golaced/Moco-8-OpenSourced-Quadruped-Robot/support_file/img_file1/a8.jpg

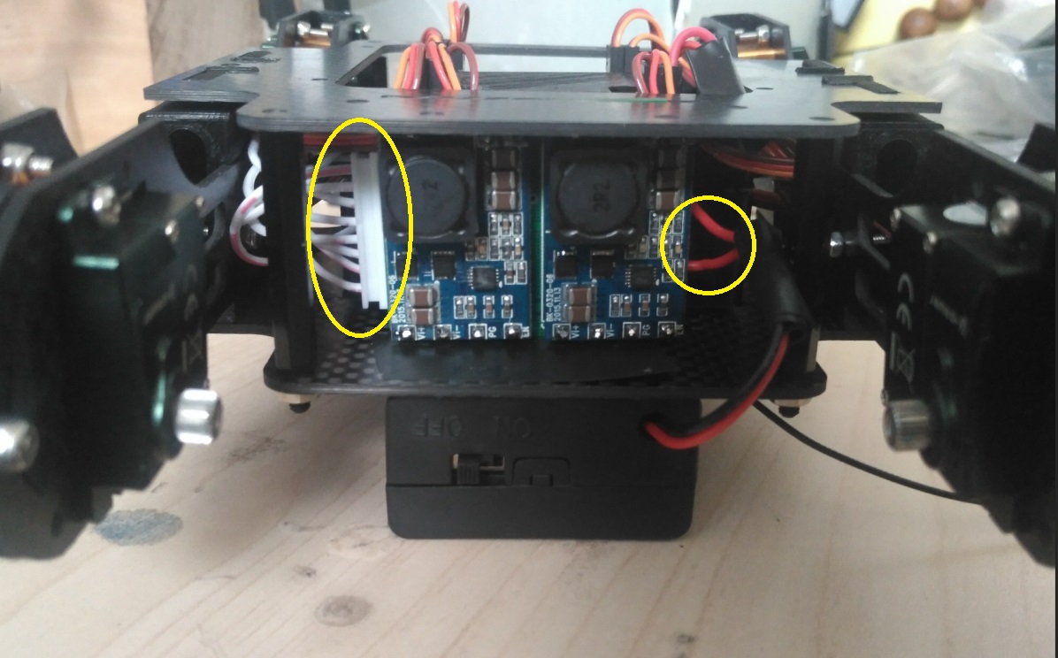
support_file/img_file1/a8.jpg
