golaced/Moco-8-OpenSourced-Quadruped-Robot/support_file/img_file1/a10.JPG

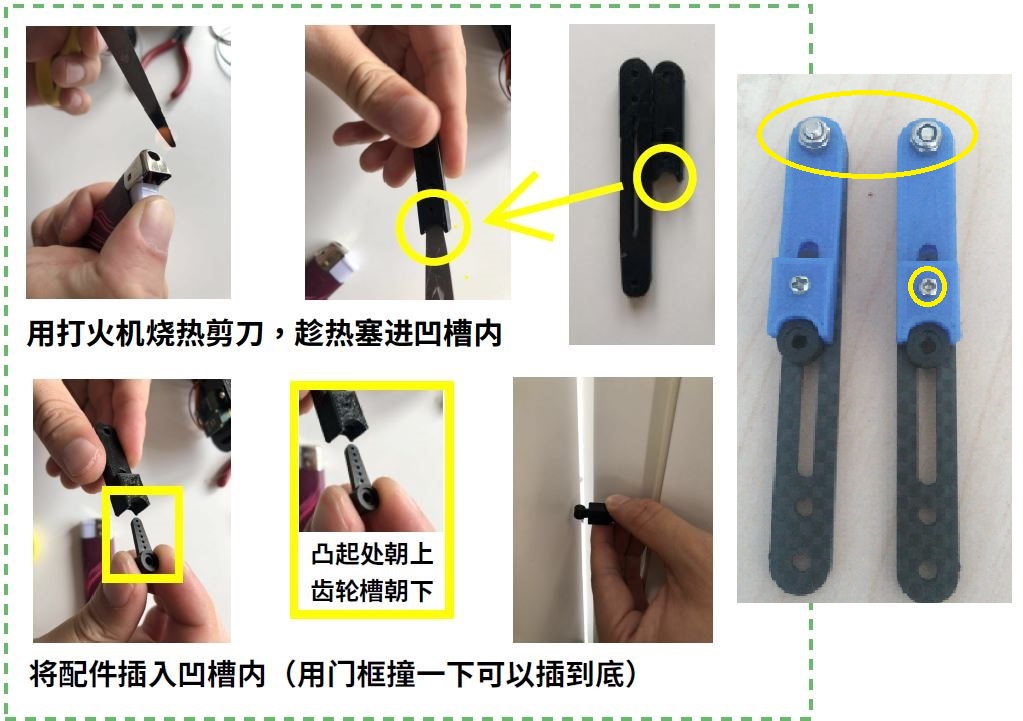
support_file/img_file1/a10.JPG
