golaced/Moco-8-OpenSourced-Quadruped-Robot/support_file/img_file1/fc5.jpg

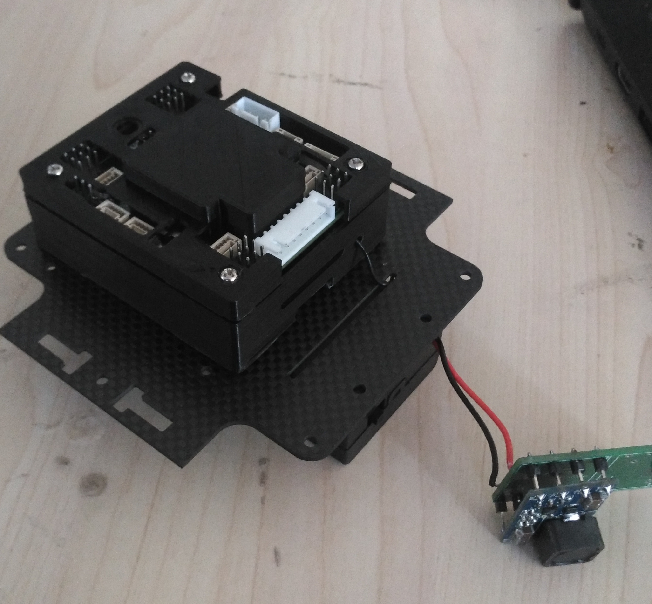
support_file/img_file1/fc5.jpg
