golaced/Moco-8-OpenSourced-Quadruped-Robot/support_file/img_file1/leg_end.jpg

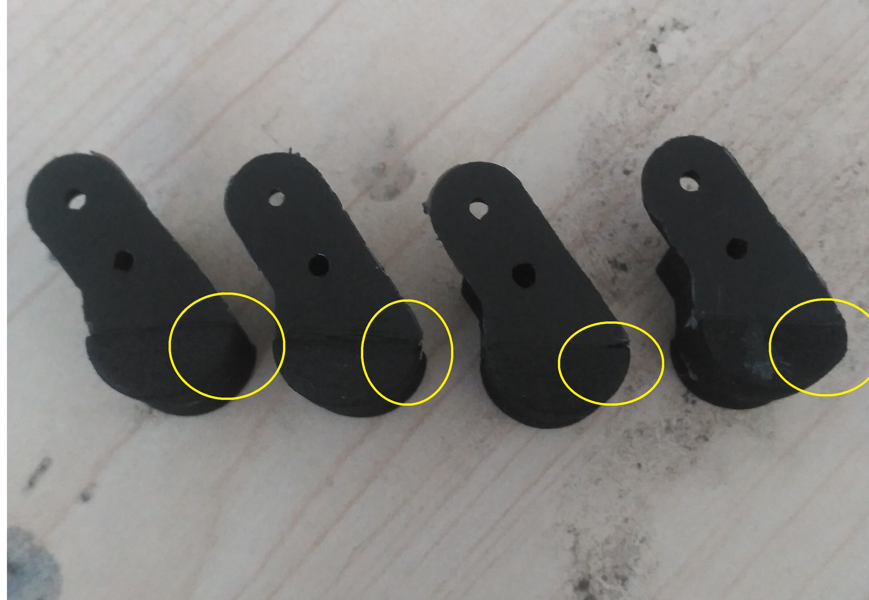
support_file/img_file1/leg_end.jpg
