golaced/Moco-8-OpenSourced-Quadruped-Robot/support_file/img_file/cap2.JPG

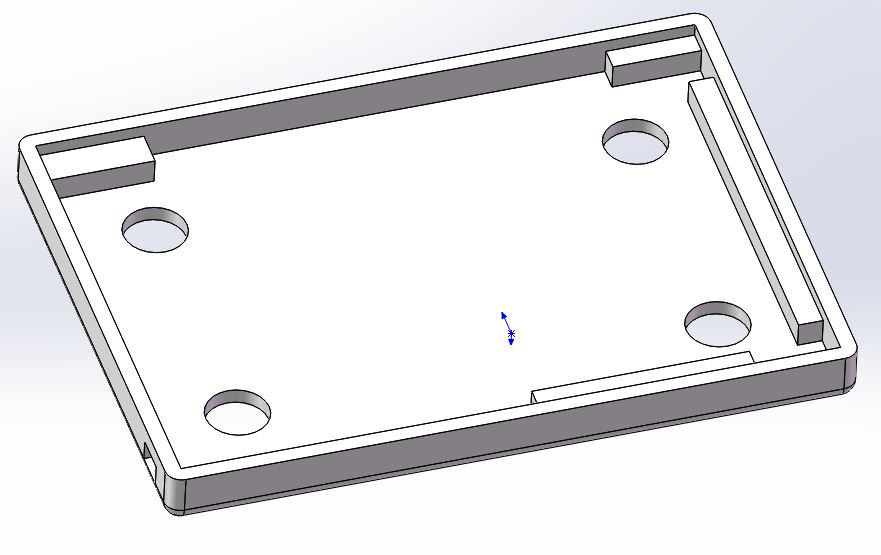
support_file/img_file/cap2.JPG
