golaced/Moco-8-OpenSourced-Quadruped-Robot/support_file/img_file/cap3.JPG

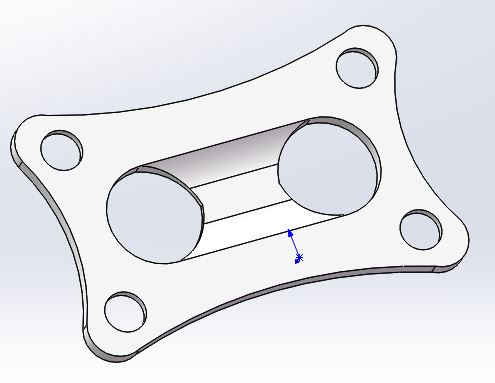
support_file/img_file/cap3.JPG
