golaced/Moco-8-OpenSourced-Quadruped-Robot/support_file/img_file/CH.jpg

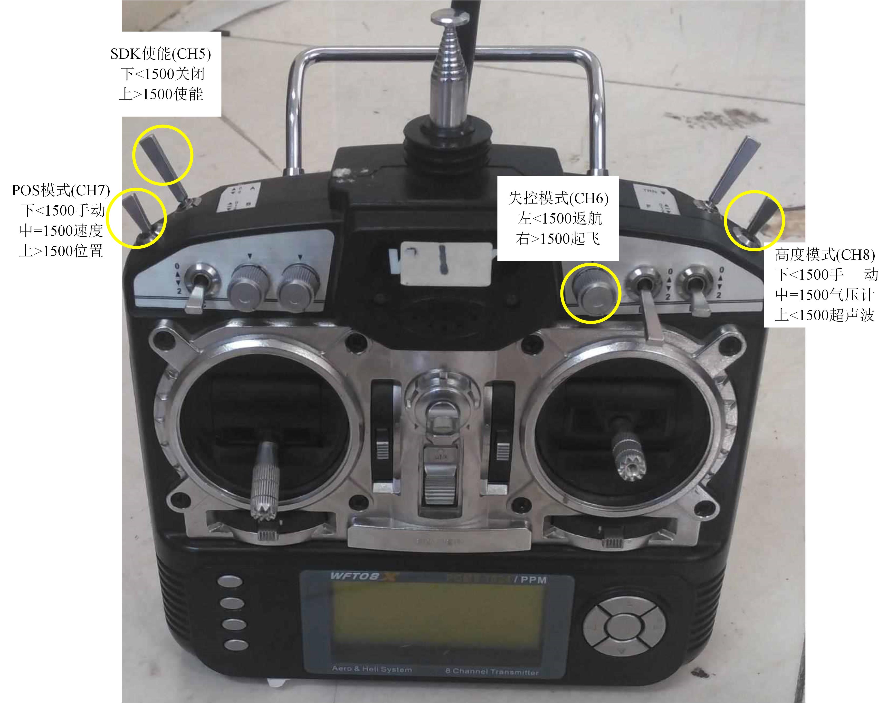
support_file/img_file/CH.jpg
