golaced/Moco-8-OpenSourced-Quadruped-Robot/support_file/img_file/dmz.JPG

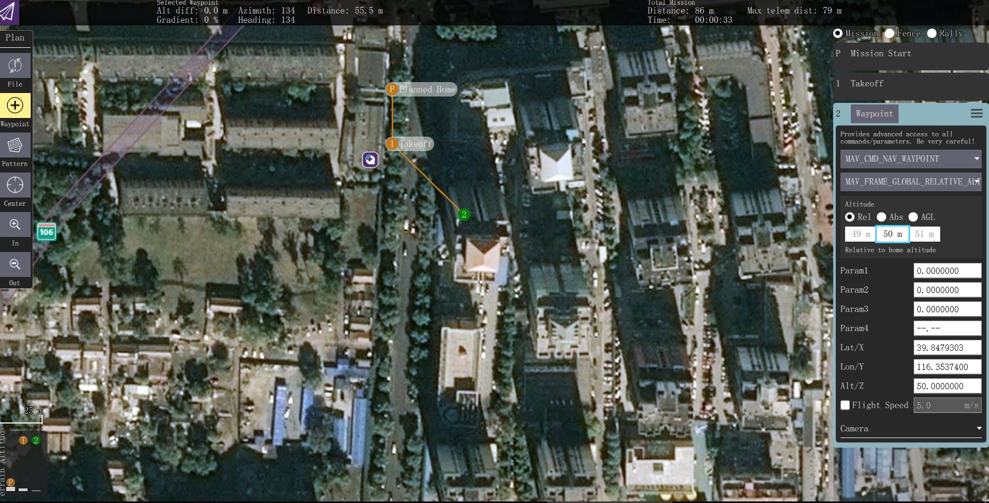
support_file/img_file/dmz.JPG
