golaced/Moco-8-OpenSourced-Quadruped-Robot/support_file/img_file/drone.jpg

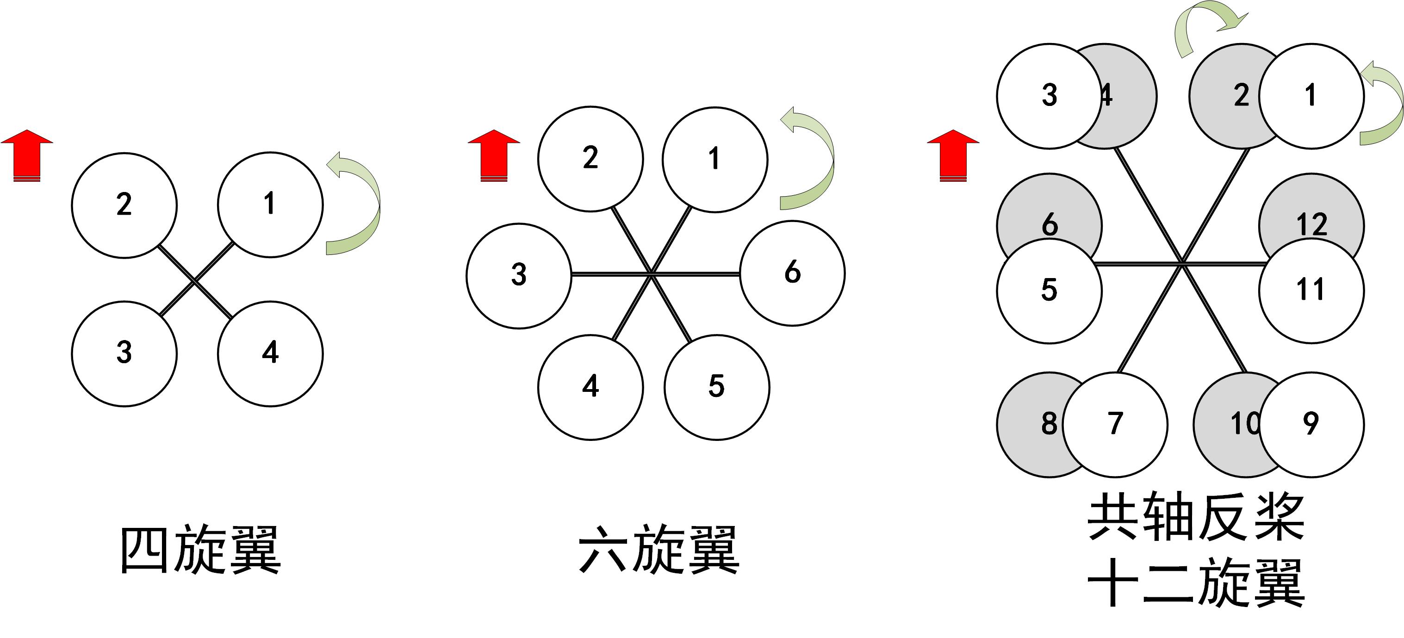
support_file/img_file/drone.jpg
