golaced/Moco-8-OpenSourced-Quadruped-Robot/support_file/img_file/fc.jpg

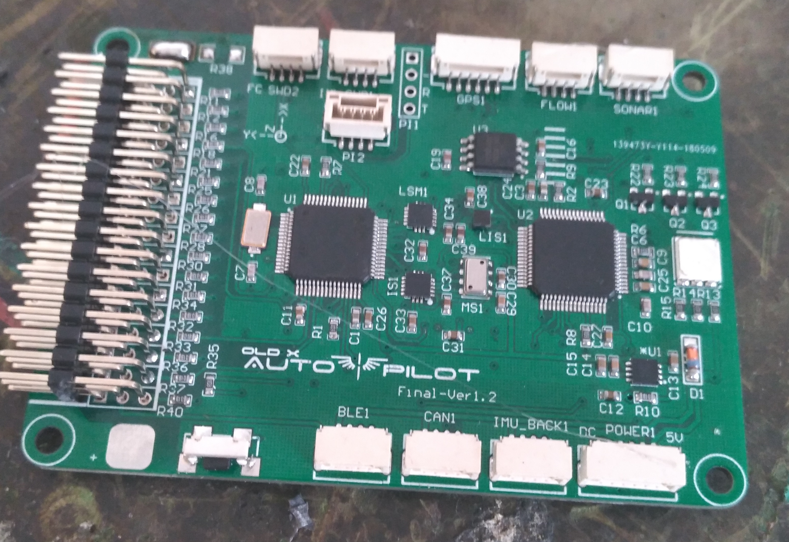
support_file/img_file/fc.jpg
