golaced/Moco-8-OpenSourced-Quadruped-Robot/support_file/img_file/pcb.jpg

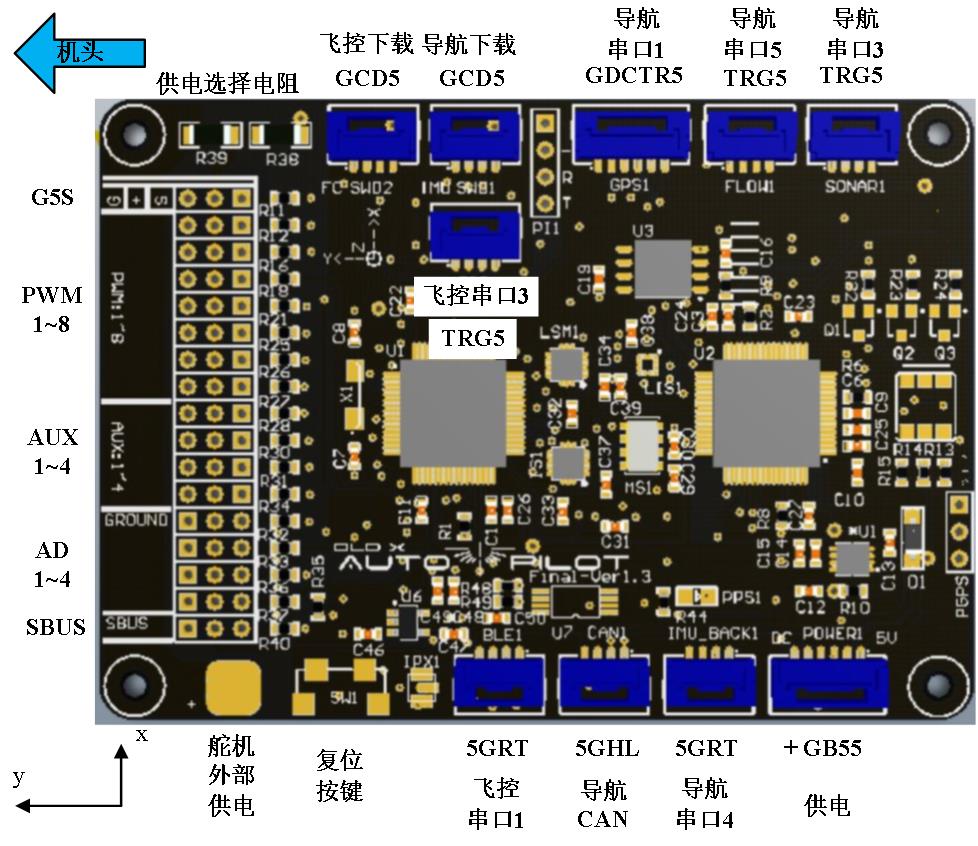
support_file/img_file/pcb.jpg
