golaced/Moco-8-OpenSourced-Quadruped-Robot/support_file/img_file/pcb_fc.JPG

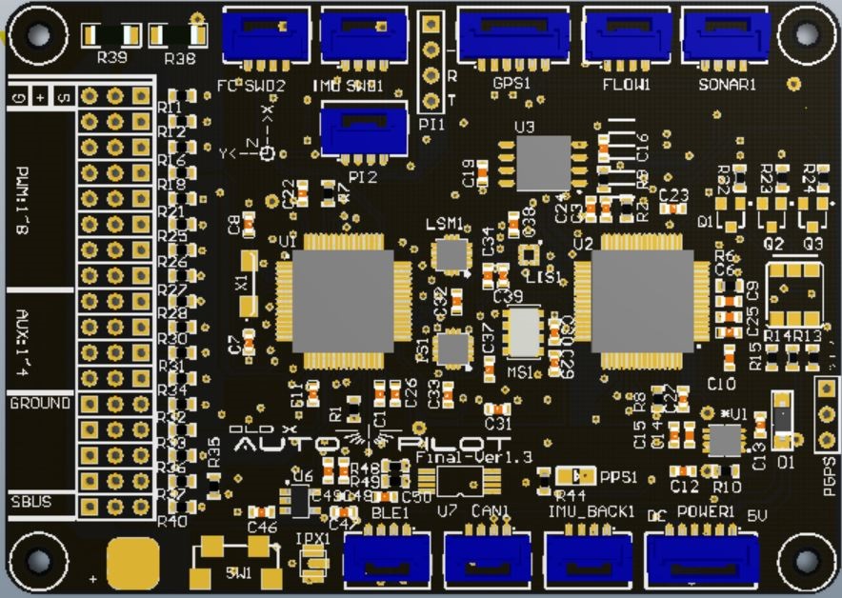
support_file/img_file/pcb_fc.JPG
