golaced/Moco-8-OpenSourced-Quadruped-Robot/quadruped/3D打印测试机架/两轴云台1.STL

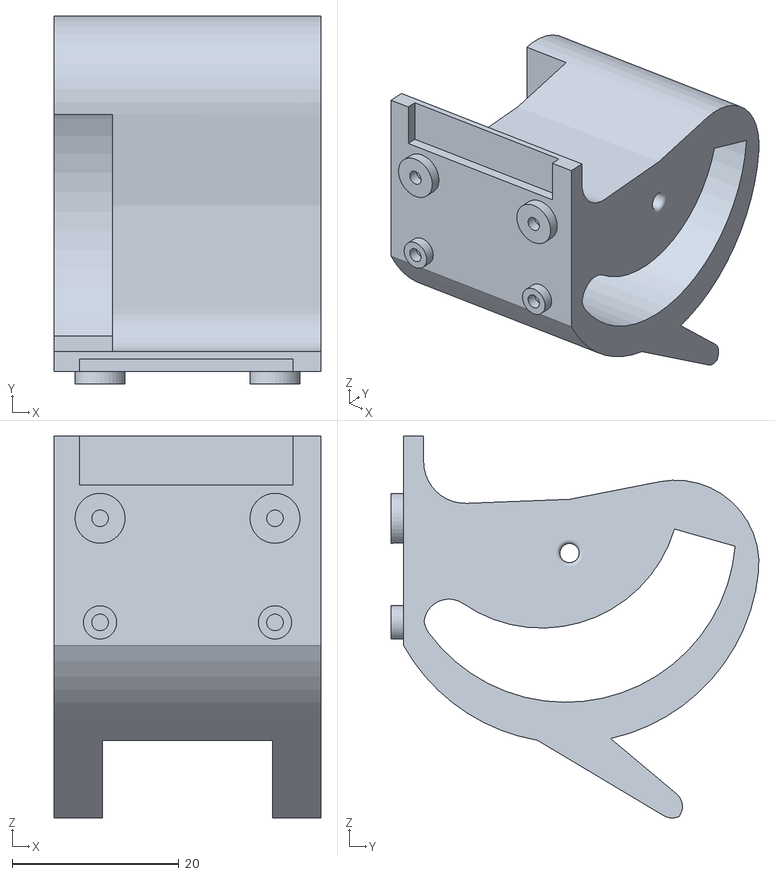
[picture p53: CAD file, 2020-11-28]
quadruped/3D打印测试机架/两轴云台1.STL
32.0 x 44.1 x 45.9
