golaced/Moco-8-OpenSourced-Quadruped-Robot/quadruped/3D打印测试机架/相机支撑可调1.STL

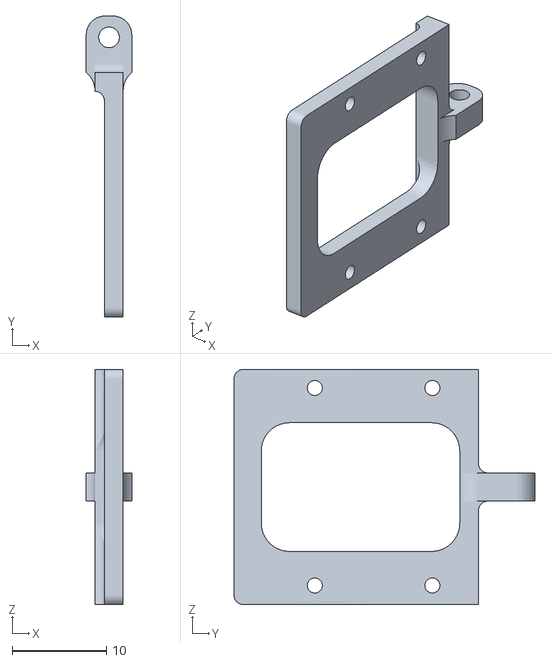
[picture p54: CAD file, 2020-11-28]
quadruped/3D打印测试机架/相机支撑可调1.STL
4.85 x 32.0 x 25.0
