golaced/Moco-8-OpenSourced-Quadruped-Robot/quadruped/3D打印测试机架/两轴云台4.STL

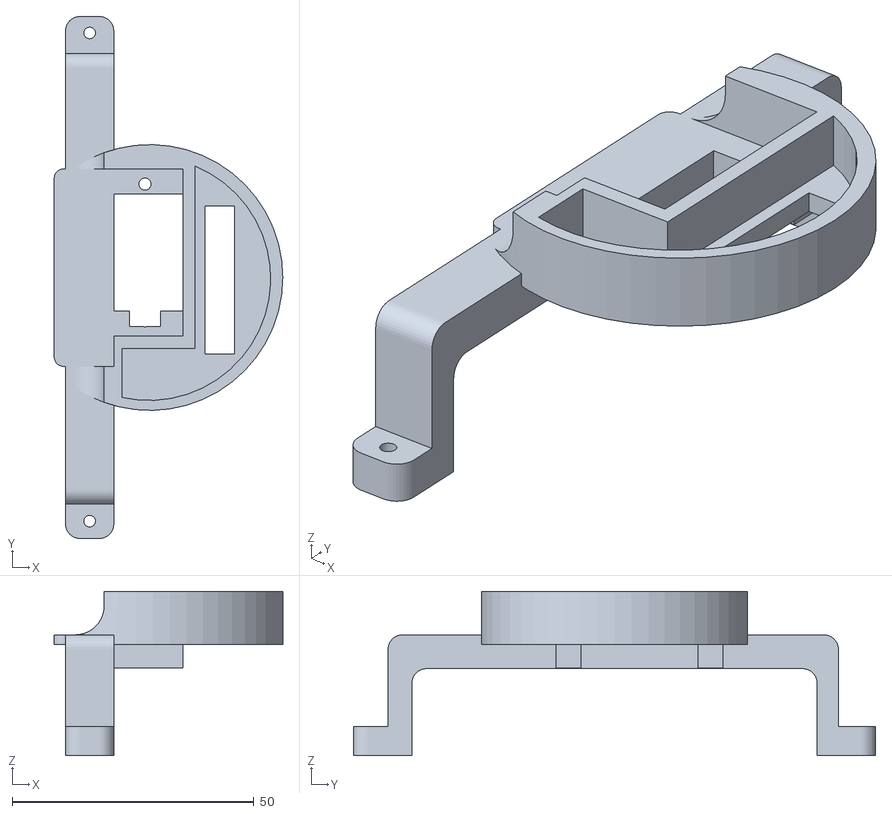
[picture p55: CAD file, 2020-11-28]
quadruped/3D打印测试机架/两轴云台4.STL
47.3 x 108.0 x 34.0
