golaced/Moco-8-OpenSourced-Quadruped-Robot/firmware/遥控器/User/usart/usart.c

#include "usart.h"
#include "stm32f10x_it.h"
#include "stm32f10x_dma.h"
#include "des.h"	
#include "head.h"	
#include "rtc.h"
#include "math.h"
/******************************************************************************/
uint8_t SendBuff[SENDBUFF_SIZE]={' ','D','M','A','1',' '};//数组【0】无法使用
u8 uart_test[4]={0,0,0,0}; 
u8 dma_can_tx=1;
u8 Addr_485=0;
void USART_ON(u8 uart_num,u32 baud,u8 m_irq,u8 s_irq)
{
	GPIO_InitTypeDef GPIO_InitStructure;
	USART_InitTypeDef USART_InitStructure;
		NVIC_InitTypeDef NVIC_InitStructure; 
		/* Configure the NVIC Preemption Priority Bits */  
	NVIC_PriorityGroupConfig(NVIC_PriorityGroup_2);
	/* config USART clock */
	if (uart_num == 1)
		RCC_APB2PeriphClockCmd(RCC_APB2Periph_USART1, ENABLE);
	else if(uart_num==2)
		RCC_APB1PeriphClockCmd(RCC_APB1Periph_USART2, ENABLE);
	else if(uart_num==3)									
		RCC_APB1PeriphClockCmd(RCC_APB1Periph_USART3, ENABLE);
	
		if (uart_num == 1)
		RCC_APB2PeriphClockCmd(RCC_APB2Periph_GPIOA, ENABLE);
	else if(uart_num==2)
		RCC_APB2PeriphClockCmd(RCC_APB2Periph_GPIOA, ENABLE);
	else if(uart_num==3)									
		RCC_APB2PeriphClockCmd(RCC_APB2Periph_GPIOB, ENABLE);
	
	
		if (uart_num == 1)
		{	/* USART GPIO config */
	/* Configure USART Tx as alternate function push-pull */
	GPIO_InitStructure.GPIO_Pin = GPIO_Pin_9;
	GPIO_InitStructure.GPIO_Mode = GPIO_Mode_AF_PP;
	GPIO_InitStructure.GPIO_Speed = GPIO_Speed_50MHz;
	GPIO_Init(GPIOA, &GPIO_InitStructure);    
	/* Configure USART Rx as input floating */
	GPIO_InitStructure.GPIO_Pin = GPIO_Pin_10;
	GPIO_InitStructure.GPIO_Mode = GPIO_Mode_IN_FLOATING;
	GPIO_Init(GPIOA, &GPIO_InitStructure);}
	else if(uart_num==2)
			{	/* USART GPIO config */
	/* Configure USART Tx as alternate function push-pull */
	GPIO_InitStructure.GPIO_Pin = GPIO_Pin_2;
	GPIO_InitStructure.GPIO_Mode = GPIO_Mode_AF_PP;
	GPIO_InitStructure.GPIO_Speed = GPIO_Speed_50MHz;
	GPIO_Init(GPIOA, &GPIO_InitStructure);    
	/* Configure USART Rx as input floating */
	GPIO_InitStructure.GPIO_Pin = GPIO_Pin_3;
	GPIO_InitStructure.GPIO_Mode = GPIO_Mode_IN_FLOATING;
	GPIO_Init(GPIOA, &GPIO_InitStructure);}
	else if(uart_num==3)									
				{	/* USART GPIO config */
	/* Configure USART Tx as alternate function push-pull */
	GPIO_InitStructure.GPIO_Pin = GPIO_Pin_10;
	GPIO_InitStructure.GPIO_Mode = GPIO_Mode_AF_PP;
	GPIO_InitStructure.GPIO_Speed = GPIO_Speed_50MHz;
	GPIO_Init(GPIOB, &GPIO_InitStructure);    
	/* Configure USART Rx as input floating */
	GPIO_InitStructure.GPIO_Pin = GPIO_Pin_11;
	GPIO_InitStructure.GPIO_Mode = GPIO_Mode_IN_FLOATING;
	GPIO_Init(GPIOB, &GPIO_InitStructure);}

	
	USART_InitStructure.USART_BaudRate = baud;
	USART_InitStructure.USART_WordLength = USART_WordLength_8b;
	USART_InitStructure.USART_StopBits = USART_StopBits_1;
	USART_InitStructure.USART_Parity = USART_Parity_No ;
	USART_InitStructure.USART_HardwareFlowControl = USART_HardwareFlowControl_None;
	USART_InitStructure.USART_Mode = USART_Mode_Rx | USART_Mode_Tx;
	if (uart_num == 1)
	{USART_Init(USART1, &USART_InitStructure);
		USART_ITConfig(USART1, USART_IT_RXNE, ENABLE);
   	USART_Cmd(USART1, ENABLE);}
	else if(uart_num==2)
		{USART_Init(USART2, &USART_InitStructure);
		USART_ITConfig(USART2, USART_IT_RXNE, ENABLE);
   	USART_Cmd(USART2, ENABLE);}
	else if(uart_num==3)									
			{USART_Init(USART3, &USART_InitStructure);
		USART_ITConfig(USART3, USART_IT_RXNE, ENABLE);
   	USART_Cmd(USART3, ENABLE);}
	
		NVIC_PriorityGroupConfig(NVIC_PriorityGroup_2);
if (uart_num == 1)
	{/* Enable the USARTy Interrupt */
	NVIC_InitStructure.NVIC_IRQChannel = USART1_IRQn;	 
	NVIC_InitStructure.NVIC_IRQChannelPreemptionPriority = m_irq;
	NVIC_InitStructure.NVIC_IRQChannelSubPriority = s_irq;
	NVIC_InitStructure.NVIC_IRQChannelCmd = ENABLE;
	NVIC_Init(&NVIC_InitStructure);}
	else if(uart_num==2)
		{/* Enable the USARTy Interrupt */
	NVIC_InitStructure.NVIC_IRQChannel = USART2_IRQn;	 
	NVIC_InitStructure.NVIC_IRQChannelPreemptionPriority = m_irq;
	NVIC_InitStructure.NVIC_IRQChannelSubPriority = s_irq;
	NVIC_InitStructure.NVIC_IRQChannelCmd = ENABLE;
	NVIC_Init(&NVIC_InitStructure);}
	else if(uart_num==3)									
		{/* Enable the USARTy Interrupt */
	NVIC_InitStructure.NVIC_IRQChannel = USART3_IRQn;	 
	NVIC_InitStructure.NVIC_IRQChannelPreemptionPriority = m_irq;
	NVIC_InitStructure.NVIC_IRQChannelSubPriority = s_irq;
	NVIC_InitStructure.NVIC_IRQChannelCmd = ENABLE;
	NVIC_Init(&NVIC_InitStructure);}
	

}

void USART1_DMA_Config(void)
{
		DMA_InitTypeDef DMA_InitStructure;
	
		/*开启DMA时钟*/
		RCC_AHBPeriphClockCmd(RCC_AHBPeriph_DMA1, ENABLE);	
		//NVIC_Config();	   			//配置DMA中断

		/*设置DMA源：串口数据寄存器地址*/
		DMA_InitStructure.DMA_PeripheralBaseAddr = USART1_DR_Base;	   

		/*内存地址(要传输的变量的指针)-----------------------分配数组*/
		DMA_InitStructure.DMA_MemoryBaseAddr = (u32)SendBuff;

		/*方向：从内存到外设*/		
		DMA_InitStructure.DMA_DIR = DMA_DIR_PeripheralDST;	

		/*传输大小DMA_BufferSize=SENDBUFF_SIZE*/	
		DMA_InitStructure.DMA_BufferSize = SENDBUFF_SIZE;

		/*外设地址不增*/	    
		DMA_InitStructure.DMA_PeripheralInc = DMA_PeripheralInc_Disable; 

		/*内存地址自增*/
		DMA_InitStructure.DMA_MemoryInc = DMA_MemoryInc_Enable;	

		/*外设数据单位*/	
		DMA_InitStructure.DMA_PeripheralDataSize = DMA_PeripheralDataSize_Byte;

		/*内存数据单位 8bit*/
		DMA_InitStructure.DMA_MemoryDataSize = DMA_MemoryDataSize_Byte;	 

		/*DMA模式：不断循环*/
		//DMA_InitStructure.DMA_Mode = DMA_Mode_Normal ;
		DMA_InitStructure.DMA_Mode = DMA_Mode_Circular;	 

		/*优先级：中*/	
		DMA_InitStructure.DMA_Priority = DMA_Priority_Medium;  

		/*禁止内存到内存的传输	*/
		DMA_InitStructure.DMA_M2M = DMA_M2M_Disable;

		/*配置DMA1的4通道*/		   
		DMA_Init(DMA1_Channel4, &DMA_InitStructure); 	   
		
		/*使能DMA*/
		DMA_Cmd (DMA1_Channel4,ENABLE);					
		//DMA_ITConfig(DMA1_Channel4,DMA_IT_TC,ENABLE);  //配置DMA发送完成后产生中断
}


void USART2_DMA_Config(void)
{	NVIC_InitTypeDef NVIC_InitStructure; 
		DMA_InitTypeDef DMA_InitStructure;
	
		/*开启DMA时钟*/
		RCC_AHBPeriphClockCmd(RCC_AHBPeriph_DMA1, ENABLE);	
		//NVIC_Config();	   			//配置DMA中断

		/*设置DMA源：串口数据寄存器地址*/
		DMA_InitStructure.DMA_PeripheralBaseAddr = USART2_DR_Base;	   

		/*内存地址(要传输的变量的指针)-----------------------分配数组*/
		DMA_InitStructure.DMA_MemoryBaseAddr = (u32)SendBuff;

		/*方向：从内存到外设*/		
		DMA_InitStructure.DMA_DIR = DMA_DIR_PeripheralDST;	

		/*传输大小DMA_BufferSize=SENDBUFF_SIZE*/	
		DMA_InitStructure.DMA_BufferSize = SENDBUFF_SIZE;

		/*外设地址不增*/	    
		DMA_InitStructure.DMA_PeripheralInc = DMA_PeripheralInc_Disable; 

		/*内存地址自增*/
		DMA_InitStructure.DMA_MemoryInc = DMA_MemoryInc_Enable;	

		/*外设数据单位*/	
		DMA_InitStructure.DMA_PeripheralDataSize = DMA_PeripheralDataSize_Byte;

		/*内存数据单位 8bit*/
		DMA_InitStructure.DMA_MemoryDataSize = DMA_MemoryDataSize_Byte;	 

		/*DMA模式：不断循环*/
		DMA_InitStructure.DMA_Mode = DMA_Mode_Normal ;
		//DMA_InitStructure.DMA_Mode = DMA_Mode_Circular;	 

		/*优先级：中*/	
		DMA_InitStructure.DMA_Priority = DMA_Priority_Medium;  

		/*禁止内存到内存的传输	*/
		DMA_InitStructure.DMA_M2M = DMA_M2M_Disable;

		/*配置DMA1的4通道*/		   
		DMA_Init(DMA1_Channel7, &DMA_InitStructure); 	   
		
		/*使能DMA*/
		DMA_Cmd (DMA1_Channel7,ENABLE);					
		DMA_ITConfig(DMA1_Channel7,DMA_IT_TC,ENABLE);  //配置DMA发送完成后产生中断
		
			//DMA发送中断设置  
		NVIC_InitStructure.NVIC_IRQChannel = DMA1_Channel7_IRQn;  
		NVIC_InitStructure.NVIC_IRQChannelPreemptionPriority =0;  
		NVIC_InitStructure.NVIC_IRQChannelSubPriority = 1;  
		NVIC_InitStructure.NVIC_IRQChannelCmd = ENABLE;  
		NVIC_Init(&NVIC_InitStructure);  
}
void USART_init(void)
{
	USART_ON(1,115200,2,1);//485

//	USART2_DMA_Config();
	
}

ID CARD[MAX_SAVE];
u8 open_lock1=0;
void UsartSend(uint8_t ch)
{
	USART_SendData(USART1, (uint8_t) ch);

	/* Loop until the end of transmission */
	while (USART_GetFlagStatus(USART1, USART_FLAG_TC) == RESET)
	{}
}


void my_itoa(int num,u8* str)  
{  
    int sign = num;  
    int i = 0;  
    int j = 0;  
    char temp[100];  
    //如果是负数就去掉符号,将-1234转成1234  
    if(sign < 0)  
    {  
        num = -num;  
    }  
    //转成字符串，1234转成"4321"  
    do  
    {  
        temp[i] = num % 10 + '0';  
        num /= 10;  
        i++;  
    }while(num > 0);  
    //如果是负数的话，加个符号在末尾，如："4321-"  
    if(sign < 0)  
    {  
        temp[i++] = '-';  
    }  
    temp[i] = '\0';  
    i--;  
    //将temp数组中逆序输入到str数组中  
    //将"4321-" ====> "-1234"  
    while(i >= 0)  
    {  
        str[j] = temp[i];  
        j++;  
        i--;  
    }  
    //字符串结束标识  
    str[j] = '\0';   
}  


#define MAX_NUM 125

char RX_BUF[MAX_NUM],RX_BUF_OUT[MAX_NUM];
	
void USART3_IRQ_TASK(void)//FLOW
{
	
}

void UART_TX_CHAR(u8 sel ,char data)
{
	if(sel==1)
	{
	USART_SendData(USART1, (u8) data);
		while(USART_GetFlagStatus(USART1, USART_FLAG_TXE) == RESET)
		;
	}
	else 	if(sel==2)
	{
	USART_SendData(USART2, (u8) data);
		while(USART_GetFlagStatus(USART2, USART_FLAG_TXE) == RESET)
		;
	}
	else 	if(sel==3)
	{
	USART_SendData(USART3, (u8) data);
		while(USART_GetFlagStatus(USART3, USART_FLAG_TXE) == RESET)
		;
	}
}


/// 重定向c库函数printf到USART
int fputc(int ch, FILE *f)
{
		/* 发送一个字节数据到USART1 */
		USART_SendData(TEST_USART, (uint8_t) ch);
		
		/* 等待发送完毕 */
		while (USART_GetFlagStatus(TEST_USART, USART_FLAG_TC) == RESET);		
	
		return (ch);
}

/// 重定向c库函数scanf到USART
int fgetc(FILE *f)
{
		/* 等待串口1输入数据 */
		while (USART_GetFlagStatus(TEST_USART, USART_FLAG_RXNE) == RESET);

		return (int)USART_ReceiveData(TEST_USART);
}

/*********************************************END OF FILE**********************/
