golaced/Moco-8-OpenSourced-Quadruped-Robot/firmware/4LEG - 2AN 1.3.5开源/HARDWARE/IIC/iic_vl53.c

#include "include.h"
#include "iic_vl53.h"
#include "time.h"
#include "bat.h"
volatile u8 I2C_FastMode_VL53;
LS53 ls53[12];
u8 delay_vl53=5,ls53_connect[12];
void I2c_Soft_delay_VL53()
{ 
	__nop();__nop();__nop();
	__nop();__nop();__nop();
	__nop();__nop();__nop();
	
	if(!I2C_FastMode_VL53)
	{
		u8 i = delay_vl53;
		while(i--);
	}
}
//u8 IIC_Write_1Byte_VL53(u8 SlaveAddress,u8 REG_Address,u8 REG_data);
//u8 IIC_Read_1Byte_VL53(u8 SlaveAddress,u8 REG_Address,u8 *REG_data);
//u8 IIC_Write_nByte_VL53(u8 SlaveAddress, u8 REG_Address, u8 len, u8 *buf);
//u8 IIC_Read_nByte_VL53(u8 SlaveAddress, u8 REG_Address, u8 len, u8 *buf);

void Init_Ground_Key(void)
{
  GPIO_InitTypeDef  GPIO_InitStructure; 
  //1	
	RCC_AHB1PeriphClockCmd(ANO_RCC_I2C_VL53OD1 , ENABLE );
  GPIO_InitStructure.GPIO_Pin =  I2C_Pin_SDA_VL53O1 ;
	GPIO_InitStructure.GPIO_Mode = GPIO_Mode_IN;
	GPIO_InitStructure.GPIO_Speed = GPIO_Speed_100MHz;
	GPIO_InitStructure.GPIO_PuPd = GPIO_PuPd_UP;
  GPIO_Init(ANO_GPIO_I2C_VL53OD1, &GPIO_InitStructure);	
	//2
  GPIO_InitStructure.GPIO_Pin =  I2C_Pin_SDA_VL53O2 ;
	GPIO_InitStructure.GPIO_Mode = GPIO_Mode_IN;
	GPIO_InitStructure.GPIO_Speed = GPIO_Speed_100MHz;
	GPIO_InitStructure.GPIO_PuPd = GPIO_PuPd_UP;
  GPIO_Init(ANO_GPIO_I2C_VL53OD2, &GPIO_InitStructure);	
	//3
	RCC_AHB1PeriphClockCmd(ANO_RCC_I2C_VL53OD3 , ENABLE );
  GPIO_InitStructure.GPIO_Pin =  I2C_Pin_SDA_VL53O3 ;
	GPIO_InitStructure.GPIO_Mode = GPIO_Mode_IN;
	GPIO_InitStructure.GPIO_Speed = GPIO_Speed_100MHz;
	GPIO_InitStructure.GPIO_PuPd = GPIO_PuPd_UP;
  GPIO_Init(ANO_GPIO_I2C_VL53OD3, &GPIO_InitStructure);	
	//4
	RCC_AHB1PeriphClockCmd(ANO_RCC_I2C_VL53OD4 , ENABLE );
  GPIO_InitStructure.GPIO_Pin =  I2C_Pin_SDA_VL53O4 ;
	GPIO_InitStructure.GPIO_Mode = GPIO_Mode_IN;
	GPIO_InitStructure.GPIO_Speed = GPIO_Speed_100MHz;
	GPIO_InitStructure.GPIO_PuPd = GPIO_PuPd_UP;
  GPIO_Init(ANO_GPIO_I2C_VL53OD4, &GPIO_InitStructure);	
}	

float ground_check_time=0.008;
void Read_Ground_Key(float dt)
{
	static u8 i,ground[4];
	static u16 cnt[2][4];
	#if defined(LEG_USE_SWITCH)
	ground[0]=!(GPIO_ReadInputDataBit(ANO_GPIO_I2C_VL53OD1,I2C_Pin_SDA_VL53O1)); 
  ground[1]=!(GPIO_ReadInputDataBit(ANO_GPIO_I2C_VL53OD2,I2C_Pin_SDA_VL53O2)); 
	ground[2]=!(GPIO_ReadInputDataBit(ANO_GPIO_I2C_VL53OD3,I2C_Pin_SDA_VL53O3)); 
	ground[3]=!(GPIO_ReadInputDataBit(ANO_GPIO_I2C_VL53OD4,I2C_Pin_SDA_VL53O4)); 
	#else
	ground_check_time=0;
	ground[0]=ground_vad[1];
	ground[1]=ground_vad[2];
	ground[2]=ground_vad[3];
	ground[3]=ground_vad[4];
	#endif

	for(i=0;i<4;i++)
	{
	  if(ls53[i].mode==0&&ground[i]==1)
	   cnt[0][i]++;
		else
		 cnt[0][i]=0;
		
		if(cnt[0][i]>ground_check_time/dt)
	  	{ls53[i].mode=1;cnt[0][i]=0;}
		
	 if(ls53[i].mode==1&&ground[i]==0)
	   cnt[1][i]++;
		else
		 cnt[1][i]=0;
		
		if(cnt[1][i]>ground_check_time/dt)
	  	{ls53[i].mode=0;cnt[1][i]=0;}
	}
}


void I2c_Soft_Init_VL53(void)
{
  GPIO_InitTypeDef  GPIO_InitStructure; 
  //1
	
	RCC_AHB1PeriphClockCmd(ANO_RCC_I2C_VL53OC1 , ENABLE );
  GPIO_InitStructure.GPIO_Pin =  I2C_Pin_SCL_VL53O1 ;
	GPIO_InitStructure.GPIO_Mode = GPIO_Mode_OUT;
	GPIO_InitStructure.GPIO_OType = GPIO_OType_OD;
	GPIO_InitStructure.GPIO_Speed = GPIO_Speed_100MHz;
	GPIO_InitStructure.GPIO_PuPd = GPIO_PuPd_UP;
  GPIO_Init(ANO_GPIO_I2C_VL53OC1, &GPIO_InitStructure);	
	RCC_AHB1PeriphClockCmd(ANO_RCC_I2C_VL53OD1 , ENABLE );
  GPIO_InitStructure.GPIO_Pin =  I2C_Pin_SDA_VL53O1 ;
	GPIO_InitStructure.GPIO_Mode = GPIO_Mode_OUT;
	GPIO_InitStructure.GPIO_OType = GPIO_OType_OD;
	GPIO_InitStructure.GPIO_Speed = GPIO_Speed_100MHz;
	GPIO_InitStructure.GPIO_PuPd = GPIO_PuPd_UP;
  GPIO_Init(ANO_GPIO_I2C_VL53OD1, &GPIO_InitStructure);	
	//
	//2
	RCC_AHB1PeriphClockCmd(ANO_RCC_I2C_VL53OC2 , ENABLE );
  GPIO_InitStructure.GPIO_Pin =  I2C_Pin_SCL_VL53O2 ;
	GPIO_InitStructure.GPIO_Mode = GPIO_Mode_OUT;
	GPIO_InitStructure.GPIO_OType = GPIO_OType_OD;
	GPIO_InitStructure.GPIO_Speed = GPIO_Speed_100MHz;
	GPIO_InitStructure.GPIO_PuPd = GPIO_PuPd_UP;
  GPIO_Init(ANO_GPIO_I2C_VL53OC2, &GPIO_InitStructure);	
	RCC_AHB1PeriphClockCmd(ANO_RCC_I2C_VL53OD2 , ENABLE );
  GPIO_InitStructure.GPIO_Pin =  I2C_Pin_SDA_VL53O2 ;
	GPIO_InitStructure.GPIO_Mode = GPIO_Mode_OUT;
	GPIO_InitStructure.GPIO_OType = GPIO_OType_OD;
	GPIO_InitStructure.GPIO_Speed = GPIO_Speed_100MHz;
	GPIO_InitStructure.GPIO_PuPd = GPIO_PuPd_UP;
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
//  GPIO_Init(ANO_GPIO_I2C_VL53OC12, &GPIO_InitStructure);	
//	RCC_AHB1PeriphClockCmd(ANO_RCC_I2C_VL53OD12 , ENABLE );
//  GPIO_InitStructure.GPIO_Pin =  I2C_Pin_SDA_VL53O12 ;
//	GPIO_InitStructure.GPIO_Mode = GPIO_Mode_OUT;
//	GPIO_InitStructure.GPIO_OType = GPIO_OType_OD;
//	GPIO_InitStructure.GPIO_Speed = GPIO_Speed_100MHz;
//	GPIO_InitStructure.GPIO_PuPd = GPIO_PuPd_UP;
//  GPIO_Init(ANO_GPIO_I2C_VL53OD12, &GPIO_InitStructure);	
}

uint16_t makeuint16(int lsb, int msb)
{
    return ((msb & 0xFF) << 8) | (lsb & 0xFF);
}

int set_dis=55;
u8 READ_VL53(u8 sel){
u8 val=0;
static u8 flag1[12]={0},init,state[12] ;
u8 gbuf[16];
uint16_t count[3];
u8 DeviceRangeStatusInternal;
	
	  switch(state[sel])	
		{
			case 0:IIC_Write_1Byte_VL53(VL53L0X_Add,VL53L0X_REG_SYSRANGE_START, 0x01,sel);
			state[sel]=1;
			flag1[sel]=0;
			break;
			case 1:
				IIC_Read_1Byte_VL53(VL53L0X_Add,VL53L0X_REG_RESULT_RANGE_STATUS,&val,sel);
				if( val == 94) 
				{ ls53_connect[sel]=1;
					ls53[sel].connect=1;
					IIC_Read_nByte_VL53(VL53L0X_Add, 0x14 , 12, gbuf,sel);	
					count[0] = makeuint16(gbuf[7], gbuf[6]);
					count[1] = makeuint16(gbuf[9], gbuf[8]);
					count[2] = makeuint16(gbuf[11], gbuf[10]);
					DeviceRangeStatusInternal = ((gbuf[0] & 0x78) >> 3);

					ls53[sel].ambient= count[0];
					ls53[sel].signal= count[1];
					if(count[2]<1800){ 
					if(count[2]!=20)
					ls53[sel].distance= (count[2]);
					//ls53[sel].mode=1; 
					}else{
					//ls53[sel].mode=2;
					}	
					state[sel]=0;
					if(ls53[sel].distance<set_dis)
						ls53[sel].mode=1;
					else
						ls53[sel].mode=0;
				}	
				else
				flag1[sel]++;
				//if(flag1>10)
				if(flag1[sel]>2)
					state[sel]=0;
			break;
		}
}	 
	
	

int I2c_Soft_Start_VL53(u8 sel)
{
  switch(sel){
	case 0:
	SDA_H_VL53O1;
	SCL_H_VL53O1;
	I2c_Soft_delay_VL53();
	if(!SDA_read_VL53O1)return 0;	//SDA?????????,??
	SDA_L_VL53O1;
	I2c_Soft_delay_VL53();
	if(SDA_read_VL53O1) return 0;	//SDA??????????,??
	SDA_L_VL53O1;
	I2c_Soft_delay_VL53();
	break;
	case 1:
	SDA_H_VL53O2;
	SCL_H_VL53O2;
	I2c_Soft_delay_VL53();
	if(!SDA_read_VL53O2)return 0;	//SDA?????????,??
	SDA_L_VL53O2;
	I2c_Soft_delay_VL53();
	if(SDA_read_VL53O2) return 0;	//SDA??????????,??
	SDA_L_VL53O2;
	I2c_Soft_delay_VL53();
	break;
	case 2:
	SDA_H_VL53O3;
	SCL_H_VL53O3;
	I2c_Soft_delay_VL53();
	if(!SDA_read_VL53O3)return 0;	//SDA?????????,??
	SDA_L_VL53O3;
	I2c_Soft_delay_VL53();
	if(SDA_read_VL53O3) return 0;	//SDA??????????,??
	SDA_L_VL53O3;
	I2c_Soft_delay_VL53();
	break;
		case 3:
	SDA_H_VL53O4;
	SCL_H_VL53O4;
	I2c_Soft_delay_VL53();
	if(!SDA_read_VL53O4)return 0;	//SDA?????????,??
	SDA_L_VL53O4;
	I2c_Soft_delay_VL53();
	if(SDA_read_VL53O4) return 0;	//SDA??????????,??
	SDA_L_VL53O4;
	I2c_Soft_delay_VL53();
	break;
			case 4:
	SDA_H_VL53O5;
	SCL_H_VL53O5;
	I2c_Soft_delay_VL53();
	if(!SDA_read_VL53O5)return 0;	//SDA?????????,??
	SDA_L_VL53O5;
	I2c_Soft_delay_VL53();
	if(SDA_read_VL53O5) return 0;	//SDA??????????,??
	SDA_L_VL53O5;
	I2c_Soft_delay_VL53();
	break;
						case 5:
	SDA_H_VL53O6;
	SCL_H_VL53O6;
	I2c_Soft_delay_VL53();
	if(!SDA_read_VL53O6)return 0;	//SDA?????????,??
	SDA_L_VL53O6;
	I2c_Soft_delay_VL53();
	if(SDA_read_VL53O6) return 0;	//SDA??????????,??
	SDA_L_VL53O6;
	I2c_Soft_delay_VL53();
	break;
										case 6:
	SDA_H_VL53O7;
	SCL_H_VL53O7;
	I2c_Soft_delay_VL53();
	if(!SDA_read_VL53O7)return 0;	//SDA?????????,??
	SDA_L_VL53O7;
	I2c_Soft_delay_VL53();
	if(SDA_read_VL53O7) return 0;	//SDA??????????,??
	SDA_L_VL53O7;
	I2c_Soft_delay_VL53();
	break;
												case 7:
	SDA_H_VL53O8;
	SCL_H_VL53O8;
	I2c_Soft_delay_VL53();
	if(!SDA_read_VL53O8)return 0;	//SDA?????????,??
	SDA_L_VL53O8;
	I2c_Soft_delay_VL53();
	if(SDA_read_VL53O8) return 0;	//SDA??????????,??
	SDA_L_VL53O8;
	I2c_Soft_delay_VL53();
	break;
														case 8:
	SDA_H_VL53O9;
	SCL_H_VL53O9;
	I2c_Soft_delay_VL53();
	if(!SDA_read_VL53O9)return 0;	//SDA?????????,??
	SDA_L_VL53O9;
	I2c_Soft_delay_VL53();
	if(SDA_read_VL53O9) return 0;	//SDA??????????,??
	SDA_L_VL53O9;
	I2c_Soft_delay_VL53();
	break;
																											case 9:
	SDA_H_VL53O10;
	SCL_H_VL53O10;
	I2c_Soft_delay_VL53();
	if(!SDA_read_VL53O10)return 0;	//SDA?????????,??
	SDA_L_VL53O10;
	I2c_Soft_delay_VL53();
	if(SDA_read_VL53O10) return 0;	//SDA??????????,??
	SDA_L_VL53O10;
	I2c_Soft_delay_VL53();
	break;
																																								case 10:
	SDA_H_VL53O11;
	SCL_H_VL53O11;
	I2c_Soft_delay_VL53();
	if(!SDA_read_VL53O11)return 0;	//SDA?????????,??
	SDA_L_VL53O11;
	I2c_Soft_delay_VL53();
	if(SDA_read_VL53O11) return 0;	//SDA??????????,??
	SDA_L_VL53O11;
	I2c_Soft_delay_VL53();
	break;
																																																					case 11:
	SDA_H_VL53O12;
	SCL_H_VL53O12;
	I2c_Soft_delay_VL53();
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
      I2c_Soft_delay_VL53();
			SCL_H_VL53O12;
      I2c_Soft_delay_VL53();	
      if(SDA_read_VL53O12)
      {
        ReceiveByte|=0x01;
      }
    }
    SCL_L_VL53O12;

	if (ask)
		I2c_Soft_Ask_VL53(sel);
	else
		I2c_Soft_NoAsk_VL53(sel);  
	break;
}
    return ReceiveByte;
} 


// IIC???????
u8 IIC_Write_1Byte_VL53(u8 SlaveAddress,u8 REG_Address,u8 REG_data,u8 sel)
{
	I2c_Soft_Start_VL53(sel);
	I2c_Soft_SendByte_VL53(SlaveAddress<<1,sel);   
	if(I2c_Soft_WaitAsk_VL53(sel))
	{
		I2c_Soft_Stop_VL53(sel);
		return 1;
	}
	I2c_Soft_SendByte_VL53(REG_Address,sel);       
	I2c_Soft_WaitAsk_VL53(sel);	
	I2c_Soft_SendByte_VL53(REG_data,sel);
	I2c_Soft_WaitAsk_VL53(sel);   
	I2c_Soft_Stop_VL53(sel); 
	return 0;
}

// IIC?1????
u8 IIC_Read_1Byte_VL53(u8 SlaveAddress,u8 REG_Address,u8 *REG_data,u8 sel)
{      		
	I2c_Soft_Start_VL53(sel);
	I2c_Soft_SendByte_VL53(SlaveAddress<<1,sel); 
	if(I2c_Soft_WaitAsk_VL53(sel))
	{
		I2c_Soft_Stop_VL53(sel);
		return 1;
	}
	I2c_Soft_SendByte_VL53(REG_Address,sel);     
	I2c_Soft_WaitAsk_VL53(sel);
	I2c_Soft_Start_VL53(sel);
	I2c_Soft_SendByte_VL53(SlaveAddress<<1 | 0x01,sel);
	I2c_Soft_WaitAsk_VL53(sel);
	*REG_data= I2c_Soft_ReadByte_VL53(0,sel);
	I2c_Soft_Stop_VL53(sel);
	return 0;
}	

// IIC?n????
u8 IIC_Write_nByte_VL53(u8 SlaveAddress, u8 REG_Address, u8 len, u8 *buf,u8 sel)
{	
	I2c_Soft_Start_VL53(sel);
	I2c_Soft_SendByte_VL53(SlaveAddress<<1,sel); 
	if(I2c_Soft_WaitAsk_VL53(sel))
	{
		I2c_Soft_Stop_VL53(sel);
		return 1;
	}
	I2c_Soft_SendByte_VL53(REG_Address,sel); 
	I2c_Soft_WaitAsk_VL53(sel);
	while(len--) 
	{
		I2c_Soft_SendByte_VL53(*buf++,sel); 
		I2c_Soft_WaitAsk_VL53(sel);
	}
	I2c_Soft_Stop_VL53(sel);
	return 0;
}

// IIC?n????
u8 IIC_Read_nByte_VL53(u8 SlaveAddress, u8 REG_Address, u8 len, u8 *buf,u8 sel)
{	
	I2c_Soft_Start_VL53(sel);
	I2c_Soft_SendByte_VL53(SlaveAddress<<1,sel); 
	if(I2c_Soft_WaitAsk_VL53(sel))
	{
		I2c_Soft_Stop_VL53(sel);
		return 1;
	}
	I2c_Soft_SendByte_VL53(REG_Address,sel); 
	I2c_Soft_WaitAsk_VL53(sel);
	
	I2c_Soft_Start_VL53(sel);
	I2c_Soft_SendByte_VL53(SlaveAddress<<1 | 0x01,sel); 
	I2c_Soft_WaitAsk_VL53(sel);
	while(len) 
	{
		if(len == 1)
		{
			*buf = I2c_Soft_ReadByte_VL53(0,sel);
		}
		else
		{
			*buf = I2c_Soft_ReadByte_VL53(1,sel);
		}
		buf++;
		len--;
	}
	I2c_Soft_Stop_VL53(sel);
	return 0;
}
