golaced/Moco-8-OpenSourced-Quadruped-Robot/firmware/遥控器/User/usart/RTC.c

#include "head.h"
#include "rtc.h"

//unsigned char time_buf1[8] = {20,9,3,13,18,51,00,6};//空年月日时分秒周
//unsigned char time_buf[8] ;                         //空年月日时分秒周
#define Yanshi 5

TimeStruct Writetime;
TimeStruct Readtime;
TimeStruct Settime;
void DS1302_GPIO_Config(void)
{		
	/*定义一个GPIO_InitTypeDef类型的结构体*/
	GPIO_InitTypeDef GPIO_InitStructure;

	/*开启外设时钟*/
	RCC_APB2PeriphClockCmd(RCC_APB2Periph_GPIOB, ENABLE); 

	/*选择要控制的引脚*/															   
  	GPIO_InitStructure.GPIO_Pin = P_CLK|P_DAT|P_RST;	

	/*设置引脚模式为通用推挽输出*/
  	GPIO_InitStructure.GPIO_Mode = GPIO_Mode_Out_PP;   

	/*设置引脚速率为50MHz */   
  	GPIO_InitStructure.GPIO_Speed = GPIO_Speed_50MHz; 

	/*调用库函数，初始化*/
  	GPIO_Init(GPIOB, &GPIO_InitStructure);		  
	 
}
void IO_Output(void)
{
	GPIO_InitTypeDef GPIO_InitStructure;
	GPIO_InitStructure.GPIO_Pin =P_CLK|P_DAT|P_RST;	  //PB0 --DS18B20_SCLK
	GPIO_InitStructure.GPIO_Mode = GPIO_Mode_Out_PP; //推挽输出
	GPIO_InitStructure.GPIO_Speed = GPIO_Speed_50MHz;
	GPIO_Init(GPIOB, &GPIO_InitStructure);
}
void IO_Input(void)
{
	GPIO_InitTypeDef GPIO_InitStructure;
	GPIO_InitStructure.GPIO_Pin =P_DAT;  //PC5 DS1302 数据接口
	GPIO_InitStructure.GPIO_Mode = GPIO_Mode_IPU; //上拉输入
	GPIO_Init(GPIOB, &GPIO_InitStructure);
}	
		
//BCD处理
void BCDconvert1(TimeStruct*p)
{
	p->year	=(((p->year) /10)<<4)+(p->year) %10;
	p->month=(((p->month)/10)<<4)+(p->month)%10;
	p->day	=(((p->day)	 /10)<<4)+(p->day)  %10;
	p->week	=(((p->week) /10)<<4)+(p->week) %10;
	p->hour	=(((p->hour) /10)<<4)+(p->hour) %10;
	p->min	=(((p->min)  /10)<<4)+(p->min)  %10;
	p->sec	=(((p->sec)	 /10)<<4)+(p->sec)  %10;

}
void BCDconvert2(TimeStruct*p)
{
	p->year	=(((p->year) /16)*10)+(p->year) %16;
	p->month=(((p->month)/16)*10)+(p->month)%16;
	p->day	=(((p->day)	 /16)*10)+(p->day)  %16;
	p->week	=(((p->week) /16)*10)+(p->week) %16;
	p->hour	=(((p->hour) /16)*10)+(p->hour) %16;
	p->min	=(((p->min)	 /16)*10)+(p->min)	%16;
	p->sec	=(((p->sec)	 /16)*10)+(p->sec)	%16;

}
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
